AnthonyDiGirolamo/teensy-thumb-keyboard/images/ttb_photo_empty_front.jpg

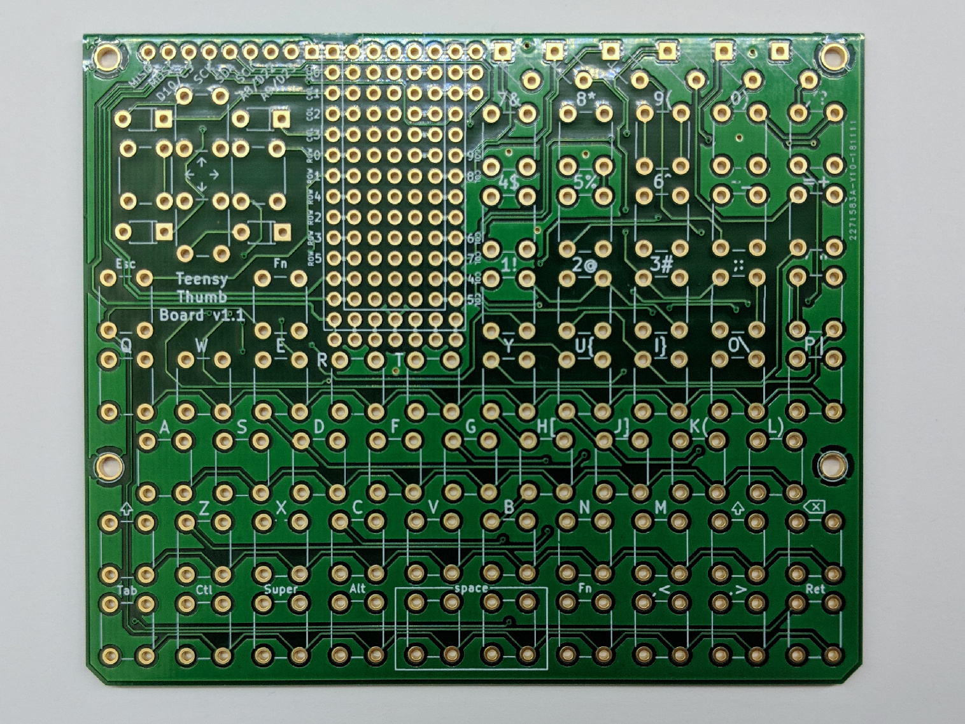
images/ttb_photo_empty_front.jpg
