AnthonyDiGirolamo/teensy-thumb-keyboard/images/ttb_photo_orientation3.jpg

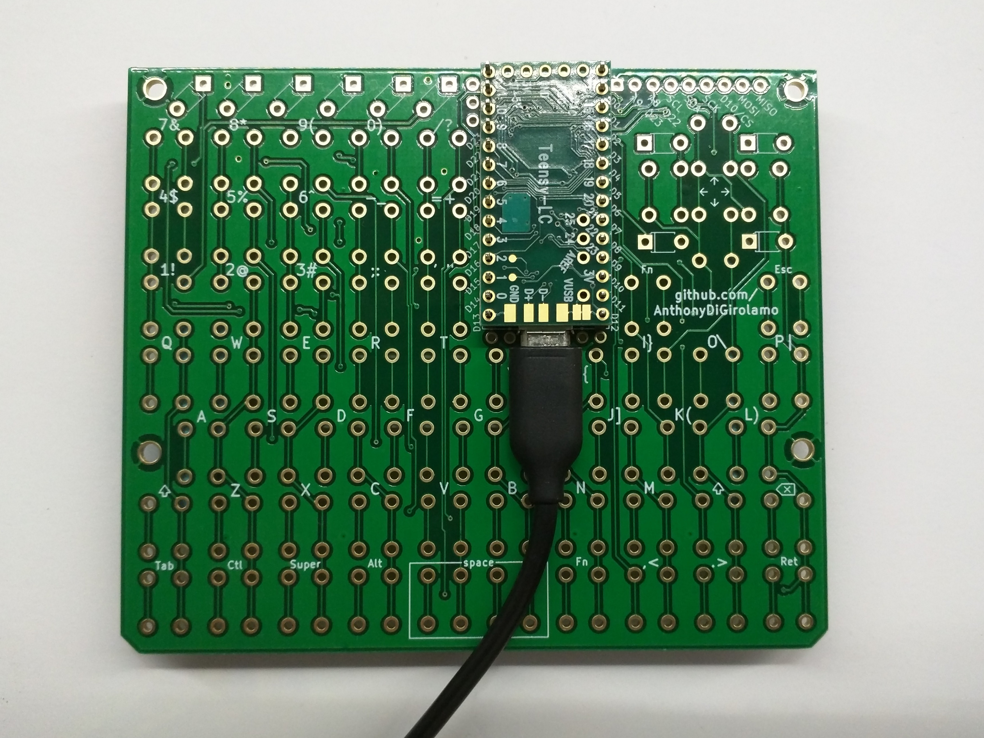
images/ttb_photo_orientation3.jpg
