AnthonyDiGirolamo/teensy-thumb-keyboard/images/ttb_photo_stack.jpg

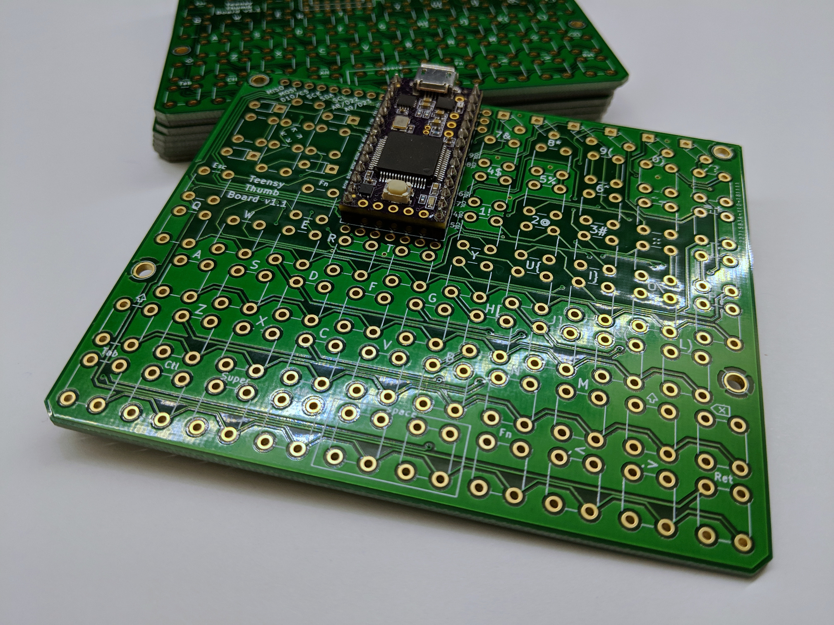
images/ttb_photo_stack.jpg
