AnthonyDiGirolamo/teensy-thumb-keyboard/images/3d_printed_faceplate.jpg

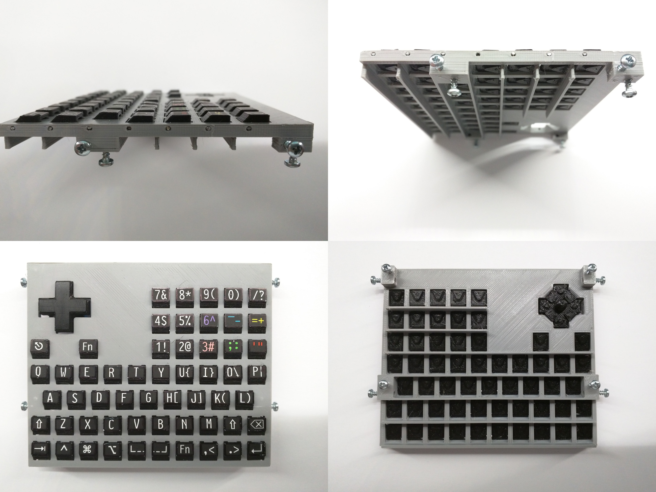
images/3d_printed_faceplate.jpg
