AnthonyDiGirolamo/teensy-thumb-keyboard/images/3d_printed_faceplate_back.jpg

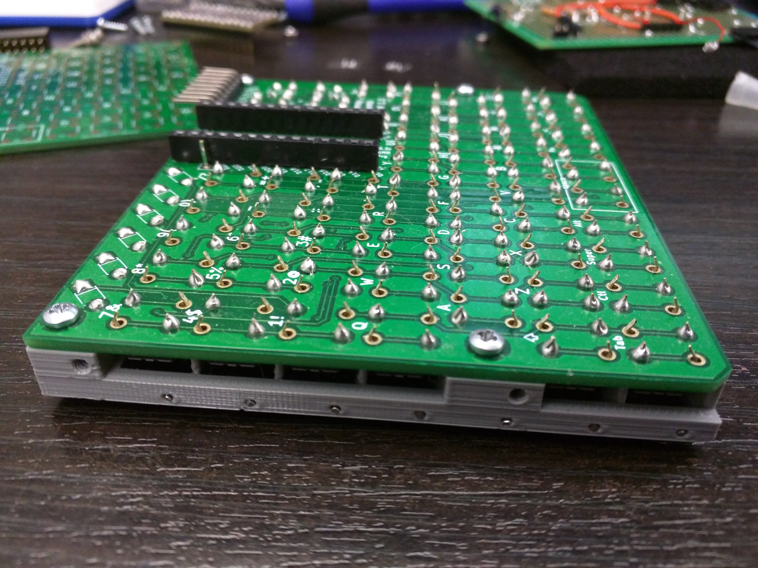
images/3d_printed_faceplate_back.jpg
