AnthonyDiGirolamo/teensy-thumb-keyboard/firmware/LayoutCommon.h

#ifndef LAYOUTCOMMON_H
#define LAYOUTCOMMON_H

#include <Arduino.h>

// Repurpose some ascii codes for arrow and modifier keys
#define ASCII_LEFT 1
#define ASCII_UP 2
#define ASCII_DOWN 3
#define ASCII_RIGHT 4

#define ASCII_CTRL 5
#define ASCII_ALT 6
#define ASCII_SUPER 7
#define ASCII_SHIFT 14
#define ASCII_SHIFT_RIGHT 15
#define ASCII_FN 16

#define ASCII_MOUSE_LEFT 17
#define ASCII_MOUSE_UP 18
#define ASCII_MOUSE_DOWN 19
#define ASCII_MOUSE_RIGHT 20

#define ASCII_MOUSE_BTN1 21
#define ASCII_MOUSE_BTN2 22
#define ASCII_MOUSE_BTN3 23
#define ASCII_FN_LOCK_TOGGLE 24

#define ASCII_MOUSE_WHEEL_UP 25
#define ASCII_MOUSE_WHEEL_RIGHT 26
#define ASCII_MOUSE_WHEEL_LEFT 28
#define ASCII_MOUSE_WHEEL_DOWN 29

#define ASCII_ESC 27

#endif
